tooyipjee/Masa/src/masa/credentials.h

#ifndef CREDENTIALS_H
#define CREDENTIALS_H

//const char* ssid     =  "VM5191158";
//const char* password =  "kgLpwnrX3jrr";
//const char* timezone =  "Europe/London";     // https://en.wikipedia.org/wiki/List_of_tz_database_time_zones
//String timezone = "America/Los_Angeles";

#endif
